Plajta/PlajTime-Hardware/3D/screw_margin.dxf

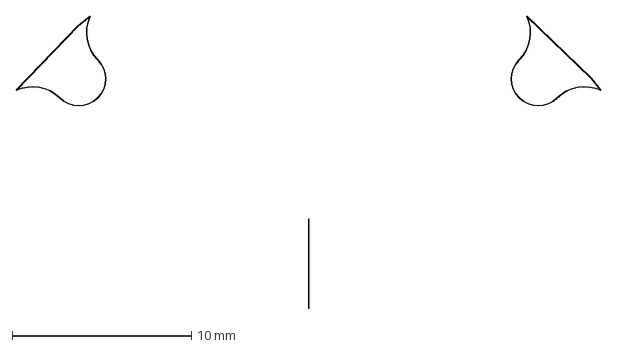
[picture p15: CAD file, 2026-02-06]
3D/screw_margin.dxf
32.6 x 16.3 mm
